pstimpel/waveformgenerator/media/IMG_20200321_164101.jpg

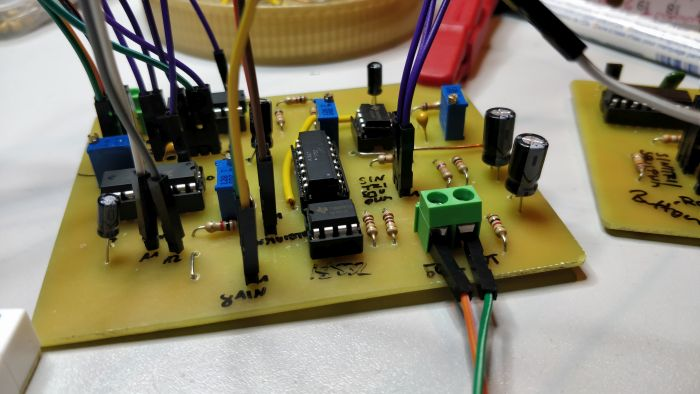
media/IMG_20200321_164101.jpg
