pstimpel/waveformgenerator/media/IMG_20200321_164112.jpg

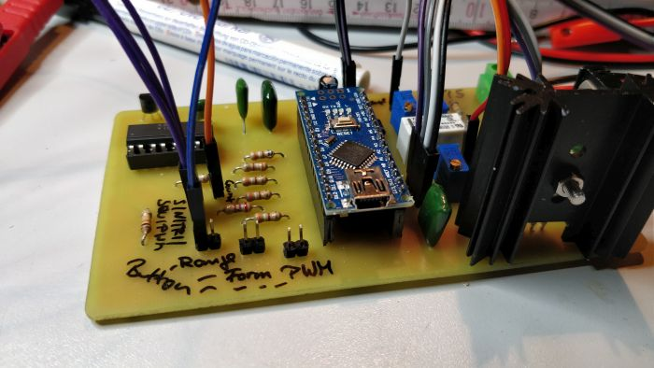
media/IMG_20200321_164112.jpg
