pstimpel/waveformgenerator/media/IMG_20200325_191447.jpg

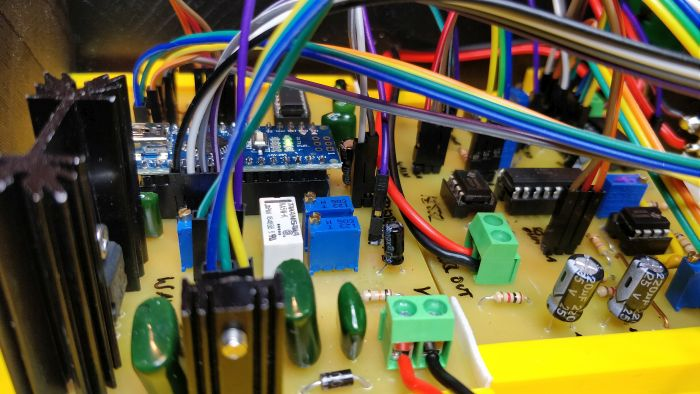
media/IMG_20200325_191447.jpg
