pstimpel/waveformgenerator/media/IMG_20200325_191454.jpg

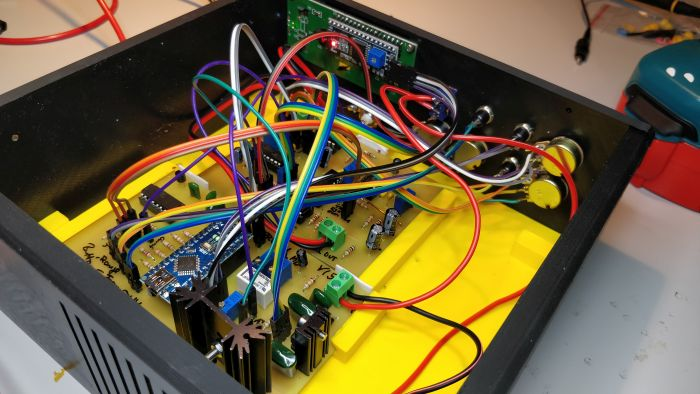
media/IMG_20200325_191454.jpg
